BTCtoolshed/TheBox/MCU Settings.png

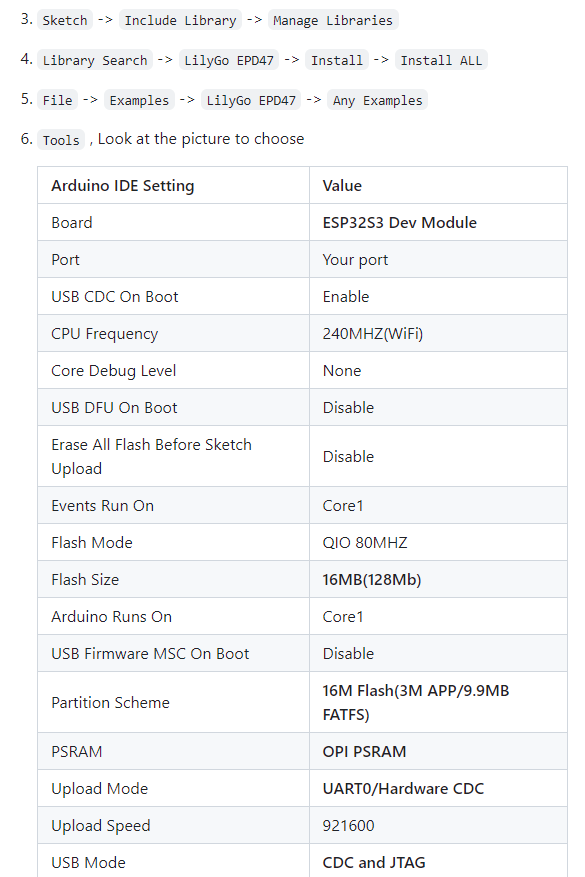
MCU Settings.png
