BTCtoolshed/TheBox/SourceLocation.png

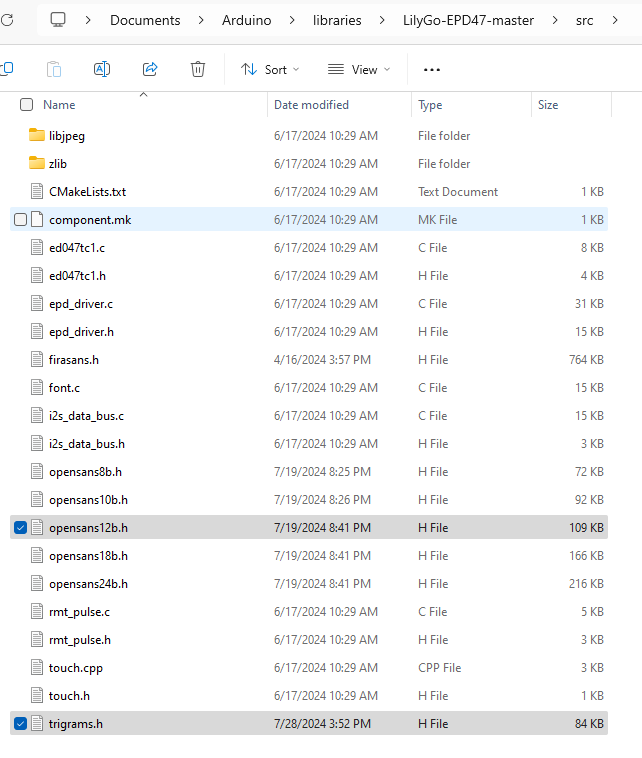
SourceLocation.png
