BTCtoolshed/TheBox/trigrams.h

const char string_0[] PROGMEM= "SPACE";
const char string_1[] PROGMEM= "a";
const char string_2[] PROGMEM= "abdomen";
const char string_3[] PROGMEM= "able/ability";
const char string_4[] PROGMEM= "abort-s-ed-ing";
const char string_5[] PROGMEM= "about";
const char string_6[] PROGMEM= "above";
const char string_7[] PROGMEM= "accident-al-s";
const char string_8[] PROGMEM= "accomplish-ed";
const char string_9[] PROGMEM= "accomplishing";
const char string_10[] PROGMEM= "ache";
const char string_11[] PROGMEM= "acknowledge";
const char string_12[] PROGMEM= "act-ion-ing-s";
const char string_13[] PROGMEM= "act-ive-ivity-s";
const char string_14[] PROGMEM= "add-ed-itional";
const char string_15[] PROGMEM= "add-ing-s";
const char string_16[] PROGMEM= "adjacent";
const char string_17[] PROGMEM= "administration";
const char string_18[] PROGMEM= "administrative";
const char string_19[] PROGMEM= "admit";
const char string_20[] PROGMEM= "advance-d-ing";
const char string_21[] PROGMEM= "after";
const char string_22[] PROGMEM= "age";
const char string_23[] PROGMEM= "agent-s";
const char string_24[] PROGMEM= "agree";
const char string_25[] PROGMEM= "air (fld/port)";
const char string_26[] PROGMEM= "airborne df";
const char string_27[] PROGMEM= "aircraft";
const char string_28[] PROGMEM= "airdrop-s";
const char string_29[] PROGMEM= "airmobile";
const char string_30[] PROGMEM= "alarm";
const char string_31[] PROGMEM= "ALE";
const char string_32[] PROGMEM= "alert-ed-ing";
const char string_33[] PROGMEM= "alive";
const char string_34[] PROGMEM= "all";
const char string_35[] PROGMEM= "alley";
const char string_36[] PROGMEM= "alt supply pt";
const char string_37[] PROGMEM= "alternate";
const char string_38[] PROGMEM= "alt ammo";
const char string_39[] PROGMEM= "altitude";
const char string_40[] PROGMEM= "am";
const char string_41[] PROGMEM= "am in pos (to)";
const char string_42[] PROGMEM= "amateur";
const char string_43[] PROGMEM= "ambulance";
const char string_44[] PROGMEM= "ambush-ed-ing";
const char string_45[] PROGMEM= "ammunition";
const char string_46[] PROGMEM= "amplitude modulation";
const char string_47[] PROGMEM= "amputate";
const char string_48[] PROGMEM= "an ";
const char string_49[] PROGMEM= "and";
const char string_50[] PROGMEM= "answer-d-ing-s";
const char string_51[] PROGMEM= "antenna";
const char string_52[] PROGMEM= "anti-";
const char string_53[] PROGMEM= "apply";
const char string_54[] PROGMEM= "approach-ed-s";
const char string_55[] PROGMEM= "approach-ing";
const char string_56[] PROGMEM= "approve-al-d-ing";
const char string_57[] PROGMEM= "approximate-ly";
const char string_58[] PROGMEM= "April";
const char string_59[] PROGMEM= "are/is";
const char string_60[] PROGMEM= "area-s";
const char string_61[] PROGMEM= "arm-s-ed";
const char string_62[] PROGMEM= "army-ies";
const char string_63[] PROGMEM= "around";
const char string_64[] PROGMEM= "arrange-d-ing";
const char string_65[] PROGMEM= "arrange-ment";
const char string_66[] PROGMEM= "arrive-al-d-ing";
const char string_67[] PROGMEM= "arrow";
const char string_68[] PROGMEM= "article";
const char string_69[] PROGMEM= "as";
const char string_70[] PROGMEM= "asap";
const char string_71[] PROGMEM= "ask";
const char string_72[] PROGMEM= "assault";
const char string_73[] PROGMEM= "assemble-d-ing";
const char string_74[] PROGMEM= "assist-ance";
const char string_75[] PROGMEM= "assist-ed-ing";
const char string_76[] PROGMEM= "at";
const char string_77[] PROGMEM= "at (once)";
const char string_78[] PROGMEM= "atlantic";
const char string_79[] PROGMEM= "attach-ed-ing";
const char string_80[] PROGMEM= "attach-ment";
const char string_81[] PROGMEM= "attack-ed-ing-s";
const char string_82[] PROGMEM= "August";
const char string_83[] PROGMEM= "authorization";
const char string_84[] PROGMEM= "authorize-d-ing";
const char string_85[] PROGMEM= "automatic";
const char string_86[] PROGMEM= "automobile";
const char string_87[] PROGMEM= "aviator/pilot";
const char string_88[] PROGMEM= "axe";
const char string_89[] PROGMEM= "axis (of)";
const char string_90[] PROGMEM= "azimuth (of)";
const char string_91[] PROGMEM= "b";
const char string_92[] PROGMEM= "back-ed-ing";
const char string_93[] PROGMEM= "bad";
const char string_94[] PROGMEM= "ball";
const char string_95[] PROGMEM= "band";
const char string_96[] PROGMEM= "bank";
const char string_97[] PROGMEM= "barbed wire";
const char string_98[] PROGMEM= "barometer";
const char string_99[] PROGMEM= "barrage-s";
const char string_100[] PROGMEM= "barrier";
const char string_101[] PROGMEM= "base-d-s-ing";
const char string_102[] PROGMEM= "battalion-s";
const char string_103[] PROGMEM= "battery charger";
const char string_104[] PROGMEM= "bed";
const char string_105[] PROGMEM= "been";
const char string_106[] PROGMEM= "beer";
const char string_107[] PROGMEM= "before";
const char string_108[] PROGMEM= "begin";
const char string_109[] PROGMEM= "below";
const char string_110[] PROGMEM= "belt";
const char string_111[] PROGMEM= "between";
const char string_112[] PROGMEM= "beyond";
const char string_113[] PROGMEM= "bike";
const char string_114[] PROGMEM= "binoculars";
const char string_115[] PROGMEM= "biological";
const char string_116[] PROGMEM= "bit";
const char string_117[] PROGMEM= "bite";
const char string_118[] PROGMEM= "bivouac-ed-ing";
const char string_119[] PROGMEM= "black";
const char string_120[] PROGMEM= "bleed";
const char string_121[] PROGMEM= "blister";
const char string_122[] PROGMEM= "block-ed-ing";
const char string_123[] PROGMEM= "blow-ing (up)";
const char string_124[] PROGMEM= "blow-n";
const char string_125[] PROGMEM= "blue";
const char string_126[] PROGMEM= "boat-s";
const char string_127[] PROGMEM= "bomb-d-r-ing-s";
const char string_128[] PROGMEM= "bone";
const char string_129[] PROGMEM= "boobytrap";
const char string_130[] PROGMEM= "book";
const char string_131[] PROGMEM= "boots";
const char string_132[] PROGMEM= "border";
const char string_133[] PROGMEM= "boundary-ies";
const char string_134[] PROGMEM= "bow";
const char string_135[] PROGMEM= "box";
const char string_136[] PROGMEM= "boy";
const char string_137[] PROGMEM= "break/broken";
const char string_138[] PROGMEM= "breakfast";
const char string_139[] PROGMEM= "breast";
const char string_140[] PROGMEM= "bridge-d-ing-s";
const char string_141[] PROGMEM= "brother";
const char string_142[] PROGMEM= "bug(s)";
const char string_143[] PROGMEM= "building-s";
const char string_144[] PROGMEM= "bulldozer";
const char string_145[] PROGMEM= "bunker-s";
const char string_146[] PROGMEM= "burst-ing-s";
const char string_147[] PROGMEM= "but";
const char string_148[] PROGMEM= "by";
const char string_149[] PROGMEM= "bypass-ed-ing-s";
const char string_150[] PROGMEM= "c";
const char string_151[] PROGMEM= "cable-s";
const char string_152[] PROGMEM= "cache";
const char string_153[] PROGMEM= "caliber";
const char string_154[] PROGMEM= "call";
const char string_155[] PROGMEM= "camera";
const char string_156[] PROGMEM= "camouflage-d";
const char string_157[] PROGMEM= "camouflage-ing";
const char string_158[] PROGMEM= "camp";
const char string_159[] PROGMEM= "can";
const char string_160[] PROGMEM= "can";
const char string_161[] PROGMEM= "canal-s";
const char string_162[] PROGMEM= "cancel-led-s";
const char string_163[] PROGMEM= "candle";
const char string_164[] PROGMEM= "capable-ity";
const char string_165[] PROGMEM= "capacity-ties";
const char string_166[] PROGMEM= "capsule";
const char string_167[] PROGMEM= "capture-d-ing";
const char string_168[] PROGMEM= "car";
const char string_169[] PROGMEM= "carry-ied-iers";
const char string_170[] PROGMEM= "casualty-ies";
const char string_171[] PROGMEM= "cave";
const char string_172[] PROGMEM= "CB radio";
const char string_173[] PROGMEM= "cease-s-d-ing";
const char string_174[] PROGMEM= "challenge-d-ing";
const char string_175[] PROGMEM= "chance";
const char string_176[] PROGMEM= "change";
const char string_177[] PROGMEM= "change cipher";
const char string_178[] PROGMEM= "channel";
const char string_179[] PROGMEM= "charge-d-s";
const char string_180[] PROGMEM= "check-d-ing-s";
const char string_181[] PROGMEM= "checkpoint";
const char string_182[] PROGMEM= "chemical-s";
const char string_183[] PROGMEM= "child-ren";
const char string_184[] PROGMEM= "church";
const char string_185[] PROGMEM= "circle";
const char string_186[] PROGMEM= "city";
const char string_187[] PROGMEM= "civilian-s";
const char string_188[] PROGMEM= "clarification(of)";
const char string_189[] PROGMEM= "class-ify";
const char string_190[] PROGMEM= "classification";
const char string_191[] PROGMEM= "clean-ed-ing";
const char string_192[] PROGMEM= "clear-ed-ance";
const char string_193[] PROGMEM= "clearing-s";
const char string_194[] PROGMEM= "close-d-ing";
const char string_195[] PROGMEM= "clothe-es-ing";
const char string_196[] PROGMEM= "coast-s-al";
const char string_197[] PROGMEM= "coffee";
const char string_198[] PROGMEM= "collapse";
const char string_199[] PROGMEM= "collect-ed-ion";
const char string_200[] PROGMEM= "collect-ing-s";
const char string_201[] PROGMEM= "column-s";
const char string_202[] PROGMEM= "combat";
const char string_203[] PROGMEM= "come-ing";
const char string_204[] PROGMEM= "comma";
const char string_205[] PROGMEM= "command-er-ed-ing-s";
const char string_206[] PROGMEM= "commit-ment";
const char string_207[] PROGMEM= "commit-ted-ing";
const char string_208[] PROGMEM= "communicate-d-ions-s";
const char string_209[] PROGMEM= "company";
const char string_210[] PROGMEM= "complete-d-ing";
const char string_211[] PROGMEM= "complete-ion";
const char string_212[] PROGMEM= "compound";
const char string_213[] PROGMEM= "compromise-d-ing";
const char string_214[] PROGMEM= "computer";
const char string_215[] PROGMEM= "concentrate-d-ing";
const char string_216[] PROGMEM= "concentrate-s-ion";
const char string_217[] PROGMEM= "condition-ed-ing";
const char string_218[] PROGMEM= "conduct-ed-ing";
const char string_219[] PROGMEM= "confidential";
const char string_220[] PROGMEM= "connect-ed-ing";
const char string_221[] PROGMEM= "connect-ion";
const char string_222[] PROGMEM= "conservation";
const char string_223[] PROGMEM= "conserve-d";
const char string_224[] PROGMEM= "consolidate-d";
const char string_225[] PROGMEM= "consolidate-ing";
const char string_226[] PROGMEM= "consolidation";
const char string_227[] PROGMEM= "contact-ed-s";
const char string_228[] PROGMEM= "contact-ing";
const char string_229[] PROGMEM= "contaminate-d";
const char string_230[] PROGMEM= "contaminate-ion-ing";
const char string_231[] PROGMEM= "continue-ation";
const char string_232[] PROGMEM= "continue-d-ing";
const char string_233[] PROGMEM= "control-ed-ing-s";
const char string_234[] PROGMEM= "conversation";
const char string_235[] PROGMEM= "convoy-s";
const char string_236[] PROGMEM= "cook";
const char string_237[] PROGMEM= "coord-s-d-ing";
const char string_238[] PROGMEM= "corporation";
const char string_239[] PROGMEM= "corps";
const char string_240[] PROGMEM= "correct (me)";
const char string_241[] PROGMEM= "correct-ed-ing";
const char string_242[] PROGMEM= "cost";
const char string_243[] PROGMEM= "could";
const char string_244[] PROGMEM= "counterattack-ed-s";
const char string_245[] PROGMEM= "counterattack-ing";
const char string_246[] PROGMEM= "counterpart";
const char string_247[] PROGMEM= "cover-ed-ing";
const char string_248[] PROGMEM= "craft";
const char string_249[] PROGMEM= "crane";
const char string_250[] PROGMEM= "critical-ly";
const char string_251[] PROGMEM= "cross-ed-ing";
const char string_252[] PROGMEM= "crossroad-s";
const char string_253[] PROGMEM= "crushed";
const char string_254[] PROGMEM= "crystal";
const char string_255[] PROGMEM= "CTCSS";
const char string_256[] PROGMEM= "culvert";
const char string_257[] PROGMEM= "cup";
const char string_258[] PROGMEM= "cut-off";
const char string_259[] PROGMEM= "CW";
const char string_260[] PROGMEM= "d";
const char string_261[] PROGMEM= "damage-d-ing";
const char string_262[] PROGMEM= "danger";
const char string_263[] PROGMEM= "dangerous";
const char string_264[] PROGMEM= "darkness";
const char string_265[] PROGMEM= "day-s/date-s";
const char string_266[] PROGMEM= "deadline-d-ing";
const char string_267[] PROGMEM= "death";
const char string_268[] PROGMEM= "December";
const char string_269[] PROGMEM= "deception";
const char string_270[] PROGMEM= "decontaminate-d-ion";
const char string_271[] PROGMEM= "decrease-d-ing";
const char string_272[] PROGMEM= "deer";
const char string_273[] PROGMEM= "defend-ed-g-s";
const char string_274[] PROGMEM= "defense-sive";
const char string_275[] PROGMEM= "degree-s";
const char string_276[] PROGMEM= "delay-ed-ing-s";
const char string_277[] PROGMEM= "delete-d-ion";
const char string_278[] PROGMEM= "deliver-ed-ing";
const char string_279[] PROGMEM= "demolition";
const char string_280[] PROGMEM= "demonstrate-d-ing";
const char string_281[] PROGMEM= "demonstrate-d-s-ion";
const char string_282[] PROGMEM= "deny-ied-ies";
const char string_283[] PROGMEM= "depart-ed-ing-ure";
const char string_284[] PROGMEM= "deploy-ed-ing";
const char string_285[] PROGMEM= "deploy-ment-s";
const char string_286[] PROGMEM= "depot";
const char string_287[] PROGMEM= "deputy-ies";
const char string_288[] PROGMEM= "designate-d";
const char string_289[] PROGMEM= "designate-ion";
const char string_290[] PROGMEM= "desk";
const char string_291[] PROGMEM= "destination";
const char string_292[] PROGMEM= "destroy-d-ing-s";
const char string_293[] PROGMEM= "detach-ed-es";
const char string_294[] PROGMEM= "detach-ment-s";
const char string_295[] PROGMEM= "determine";
const char string_296[] PROGMEM= "diesel";
const char string_297[] PROGMEM= "dig/dug (in)";
const char string_298[] PROGMEM= "dinner";
const char string_299[] PROGMEM= "direct-d-ion-ing";
const char string_300[] PROGMEM= "direction finding";
const char string_301[] PROGMEM= "disable-d-ing";
const char string_302[] PROGMEM= "disapprove-d-al";
const char string_303[] PROGMEM= "disperse-d-ing-al";
const char string_304[] PROGMEM= "displace-d-ing";
const char string_305[] PROGMEM= "displace-ment";
const char string_306[] PROGMEM= "dispose-d-al";
const char string_307[] PROGMEM= "disregard-ed-ing";
const char string_308[] PROGMEM= "distance-s";
const char string_309[] PROGMEM= "district-s";
const char string_310[] PROGMEM= "ditch";
const char string_311[] PROGMEM= "divert-ed-ion";
const char string_312[] PROGMEM= "divide";
const char string_313[] PROGMEM= "division-s";
const char string_314[] PROGMEM= "do";
const char string_315[] PROGMEM= "dog";
const char string_316[] PROGMEM= "down-ed";
const char string_317[] PROGMEM= "downed acft";
const char string_318[] PROGMEM= "drill drip";
const char string_319[] PROGMEM= "drive";
const char string_320[] PROGMEM= "driveway";
const char string_321[] PROGMEM= "drop-ping-ped";
const char string_322[] PROGMEM= "drug-s";
const char string_323[] PROGMEM= "DTMF";
const char string_324[] PROGMEM= "due";
const char string_325[] PROGMEM= "dump-ed-ing";
const char string_326[] PROGMEM= "during";
const char string_327[] PROGMEM= "e";
const char string_328[] PROGMEM= "east-ern (of)";
const char string_329[] PROGMEM= "ed";
const char string_330[] PROGMEM= "effect-ed-ing";
const char string_331[] PROGMEM= "effect-ive-s";
const char string_332[] PROGMEM= "eight";
const char string_333[] PROGMEM= "electric-al-ity";
const char string_334[] PROGMEM= "element-s";
const char string_335[] PROGMEM= "elevate-d-ion";
const char string_336[] PROGMEM= "eliminate-ed-ing-s";
const char string_337[] PROGMEM= "elk";
const char string_338[] PROGMEM= "email";
const char string_339[] PROGMEM= "embank-ment";
const char string_340[] PROGMEM= "embrace-d-ing";
const char string_341[] PROGMEM= "emergency";
const char string_342[] PROGMEM= "emplace-ment";
const char string_343[] PROGMEM= "employ-ed-ing";
const char string_344[] PROGMEM= "en";
const char string_345[] PROGMEM= "encounter-d-ing";
const char string_346[] PROGMEM= "encrypt-ed-ion";
const char string_347[] PROGMEM= "end-ed-ing";
const char string_348[] PROGMEM= "enemy";
const char string_349[] PROGMEM= "engine";
const char string_350[] PROGMEM= "engineer-d-ing-s";
const char string_351[] PROGMEM= "enlist-ed-ing";
const char string_352[] PROGMEM= "entrench-ed";
const char string_353[] PROGMEM= "envelop-ed-ing";
const char string_354[] PROGMEM= "envelope";
const char string_355[] PROGMEM= "equip-ing-s";
const char string_356[] PROGMEM= "er";
const char string_357[] PROGMEM= "error";
const char string_358[] PROGMEM= "es";
const char string_359[] PROGMEM= "escape-d-ing";
const char string_360[] PROGMEM= "estab-ed-contact at";
const char string_361[] PROGMEM= "establish";
const char string_362[] PROGMEM= "estimat-ion";
const char string_363[] PROGMEM= "estimate-d-ing";
const char string_364[] PROGMEM= "et";
const char string_365[] PROGMEM= "eta your loc";
const char string_366[] PROGMEM= "etd";
const char string_367[] PROGMEM= "evac-d-ing-ion";
const char string_368[] PROGMEM= "evasion";
const char string_369[] PROGMEM= "execute-d-ing";
const char string_370[] PROGMEM= "execute-ion-s";
const char string_371[] PROGMEM= "exercise";
const char string_372[] PROGMEM= "exhaust-ed-ing";
const char string_373[] PROGMEM= "expect-ation-s";
const char string_374[] PROGMEM= "expect-ed-ing";
const char string_375[] PROGMEM= "expedite-d-ing";
const char string_376[] PROGMEM= "explode-d-s";
const char string_377[] PROGMEM= "exploit-ed-ing";
const char string_378[] PROGMEM= "explosive-s";
const char string_379[] PROGMEM= "expose-d-ing";
const char string_380[] PROGMEM= "extend-d-g-ive";
const char string_381[] PROGMEM= "extend-extent";
const char string_382[] PROGMEM= "extend-sion";
const char string_383[] PROGMEM= "extra";
const char string_384[] PROGMEM= "extract-s-ed-ing";
const char string_385[] PROGMEM= "f";
const char string_386[] PROGMEM= "facility";
const char string_387[] PROGMEM= "fade-ed-ing";
const char string_388[] PROGMEM= "fail-ed-ing";
const char string_389[] PROGMEM= "fallout";
const char string_390[] PROGMEM= "family";
const char string_391[] PROGMEM= "far";
const char string_392[] PROGMEM= "fatal";
const char string_393[] PROGMEM= "father";
const char string_394[] PROGMEM= "favor-able-ing";
const char string_395[] PROGMEM= "favor-s-ed";
const char string_396[] PROGMEM= "February";
const char string_397[] PROGMEM= "feet/foot";
const char string_398[] PROGMEM= "FeldHell";
const char string_399[] PROGMEM= "FEMA";
const char string_400[] PROGMEM= "field-s";
const char string_401[] PROGMEM= "fight-er-ing";
const char string_402[] PROGMEM= "final";
const char string_403[] PROGMEM= "fire-d-ing-s";
const char string_404[] PROGMEM= "fish";
const char string_405[] PROGMEM= "five";
const char string_406[] PROGMEM= "flame-d-ing-s";
const char string_407[] PROGMEM= "flank-ed-ing-s";
const char string_408[] PROGMEM= "flare-d-s";
const char string_409[] PROGMEM= "fled";
const char string_410[] PROGMEM= "flesh";
const char string_411[] PROGMEM= "flexible-ity";
const char string_412[] PROGMEM= "flight";
const char string_413[] PROGMEM= "foe";
const char string_414[] PROGMEM= "fog";
const char string_415[] PROGMEM= "fold-ing";
const char string_416[] PROGMEM= "follow-ed-ing";
const char string_417[] PROGMEM= "food";
const char string_418[] PROGMEM= "for";
const char string_419[] PROGMEM= "force-s-d-ing";
const char string_420[] PROGMEM= "ford-able";
const char string_421[] PROGMEM= "forearm";
const char string_422[] PROGMEM= "forest-s";
const char string_423[] PROGMEM= "fortify-ication";
const char string_424[] PROGMEM= "fortify-ied";
const char string_425[] PROGMEM= "forward-ed-ing";
const char string_426[] PROGMEM= "found";
const char string_427[] PROGMEM= "four";
const char string_428[] PROGMEM= "fr";
const char string_429[] PROGMEM= "fracture";
const char string_430[] PROGMEM= "frag";
const char string_431[] PROGMEM= "freedom";
const char string_432[] PROGMEM= "freeze-ing";
const char string_433[] PROGMEM= "frequency modulation";
const char string_434[] PROGMEM= "frequency-ies";
const char string_435[] PROGMEM= "Friday";
const char string_436[] PROGMEM= "friend-ly";
const char string_437[] PROGMEM= "from";
const char string_438[] PROGMEM= "front-age-ally";
const char string_439[] PROGMEM= "FRS";
const char string_440[] PROGMEM= "fruit";
const char string_441[] PROGMEM= "fuel";
const char string_442[] PROGMEM= "fuse-d";
const char string_443[] PROGMEM= "future";
const char string_444[] PROGMEM= "g";
const char string_445[] PROGMEM= "gallon-s";
const char string_446[] PROGMEM= "gas-ing-ed";
const char string_447[] PROGMEM= "gasoline";
const char string_448[] PROGMEM= "gate";
const char string_449[] PROGMEM= "general-ize";
const char string_450[] PROGMEM= "generator(set)";
const char string_451[] PROGMEM= "get-ting";
const char string_452[] PROGMEM= "girl";
const char string_453[] PROGMEM= "give-n-ing";
const char string_454[] PROGMEM= "glass";
const char string_455[] PROGMEM= "GMRS";
const char string_456[] PROGMEM= "go-ing(to)";
const char string_457[] PROGMEM= "good";
const char string_458[] PROGMEM= "government";
const char string_459[] PROGMEM= "GPS";
const char string_460[] PROGMEM= "grade-d-ing";
const char string_461[] PROGMEM= "great";
const char string_462[] PROGMEM= "green";
const char string_463[] PROGMEM= "grid(coord)";
const char string_464[] PROGMEM= "ground-s-ed";
const char string_465[] PROGMEM= "group";
const char string_466[] PROGMEM= "guard-ed-ing-s";
const char string_467[] PROGMEM= "guide-ance";
const char string_468[] PROGMEM= "guide-d-s-ing";
const char string_469[] PROGMEM= "gunpowder";
const char string_470[] PROGMEM= "guns-s";
const char string_471[] PROGMEM= "h";
const char string_472[] PROGMEM= "had";
const char string_473[] PROGMEM= "halt-ed";
const char string_474[] PROGMEM= "Ham/ham";
const char string_475[] PROGMEM= "hammer";
const char string_476[] PROGMEM= "hand";
const char string_477[] PROGMEM= "handbook";
const char string_478[] PROGMEM= "handie-talkie";
const char string_479[] PROGMEM= "harass-ed-ing";
const char string_480[] PROGMEM= "harass-ment";
const char string_481[] PROGMEM= "hate";
const char string_482[] PROGMEM= "have/has";
const char string_483[] PROGMEM= "he";
const char string_484[] PROGMEM= "head-ed-ing";
const char string_485[] PROGMEM= "headphones";
const char string_486[] PROGMEM= "hear-d";
const char string_487[] PROGMEM= "heavy";
const char string_488[] PROGMEM= "held";
const char string_489[] PROGMEM= "helicopter-s";
const char string_490[] PROGMEM= "her";
const char string_491[] PROGMEM= "here";
const char string_492[] PROGMEM= "hidden";
const char string_493[] PROGMEM= "hide";
const char string_494[] PROGMEM= "high speed burst";
const char string_495[] PROGMEM= "high-er-est";
const char string_496[] PROGMEM= "highway-s";
const char string_497[] PROGMEM= "hill/mt/rise-s";
const char string_498[] PROGMEM= "him";
const char string_499[] PROGMEM= "his";
const char string_500[] PROGMEM= "hit-tin";
const char string_501[] PROGMEM= "hold-er-ing";
const char string_502[] PROGMEM= "hole";
const char string_503[] PROGMEM= "home";
const char string_504[] PROGMEM= "hospital-s";
const char string_505[] PROGMEM= "hostile";
const char string_506[] PROGMEM= "hour-s-ly";
const char string_507[] PROGMEM= "how";
const char string_508[] PROGMEM= "HQ";
const char string_509[] PROGMEM= "hundred";
const char string_510[] PROGMEM= "i";
const char string_511[] PROGMEM= "ice";
const char string_512[] PROGMEM= "identification";
const char string_513[] PROGMEM= "identify-ed";
const char string_514[] PROGMEM= "IDY";
const char string_515[] PROGMEM= "ied";
const char string_516[] PROGMEM= "ies";
const char string_517[] PROGMEM= "if";
const char string_518[] PROGMEM= "ill-ness";
const char string_519[] PROGMEM= "immediately";
const char string_520[] PROGMEM= "imminent";
const char string_521[] PROGMEM= "immobile-ize-d-ing";
const char string_522[] PROGMEM= "impact";
const char string_523[] PROGMEM= "impassible";
const char string_524[] PROGMEM= "impossible";
const char string_525[] PROGMEM= "improve-d-ing";
const char string_526[] PROGMEM= "improve-ment";
const char string_527[] PROGMEM= "improvised";
const char string_528[] PROGMEM= "in";
const char string_529[] PROGMEM= "in-accordance-with";
const char string_530[] PROGMEM= "inadequate";
const char string_531[] PROGMEM= "inch-es";
const char string_532[] PROGMEM= "incident-al-s";
const char string_533[] PROGMEM= "increase-d-ing-s";
const char string_534[] PROGMEM= "indigenous";
const char string_535[] PROGMEM= "indirect";
const char string_536[] PROGMEM= "individual";
const char string_537[] PROGMEM= "infantry";
const char string_538[] PROGMEM= "infiltrate-d-r-s";
const char string_539[] PROGMEM= "infiltrate-g-ion";
const char string_540[] PROGMEM= "inflict";
const char string_541[] PROGMEM= "inform-d-ation";
const char string_542[] PROGMEM= "infrared";
const char string_543[] PROGMEM= "ing";
const char string_544[] PROGMEM= "initial-ed-ly";
const char string_545[] PROGMEM= "insect";
const char string_546[] PROGMEM= "insert-s-ed-ing";
const char string_547[] PROGMEM= "install-d-ation";
const char string_548[] PROGMEM= "instrumental";
const char string_549[] PROGMEM= "intact";
const char string_550[] PROGMEM= "intend-ed-tion";
const char string_551[] PROGMEM= "intercept-d-or";
const char string_552[] PROGMEM= "intercept-ion-s";
const char string_553[] PROGMEM= "interfere-d-ing";
const char string_554[] PROGMEM= "interfere-nce";
const char string_555[] PROGMEM= "internal";
const char string_556[] PROGMEM= "interrogate-d";
const char string_557[] PROGMEM= "interrogate-ion";
const char string_558[] PROGMEM= "intersection";
const char string_559[] PROGMEM= "interval";
const char string_560[] PROGMEM= "is";
const char string_561[] PROGMEM= "isolate-d-ing";
const char string_562[] PROGMEM= "issue-d-ing-s";
const char string_563[] PROGMEM= "it";
const char string_564[] PROGMEM= "item-s";
const char string_565[] PROGMEM= "j";
const char string_566[] PROGMEM= "jacket";
const char string_567[] PROGMEM= "jam-med-ing";
const char string_568[] PROGMEM= "January";
const char string_569[] PROGMEM= "jeep";
const char string_570[] PROGMEM= "job";
const char string_571[] PROGMEM= "join-ed-ing";
const char string_572[] PROGMEM= "joint";
const char string_573[] PROGMEM= "July";
const char string_574[] PROGMEM= "jump-ed-ing (off)";
const char string_575[] PROGMEM= "junction-s(road)";
const char string_576[] PROGMEM= "June";
const char string_577[] PROGMEM= "jury";
const char string_578[] PROGMEM= "just";
const char string_579[] PROGMEM= "k";
const char string_580[] PROGMEM= "keep-s-ing";
const char string_581[] PROGMEM= "kerosene";
const char string_582[] PROGMEM= "key";
const char string_583[] PROGMEM= "kidney";
const char string_584[] PROGMEM= "kidney";
const char string_585[] PROGMEM= "kill";
const char string_586[] PROGMEM= "kill";
const char string_587[] PROGMEM= "killed in act";
const char string_588[] PROGMEM= "kilometer-s";
const char string_589[] PROGMEM= "kit";
const char string_590[] PROGMEM= "knife";
const char string_591[] PROGMEM= "knot";
const char string_592[] PROGMEM= "know-n-ing";
const char string_593[] PROGMEM= "knowledge";
const char string_594[] PROGMEM= "L";
const char string_595[] PROGMEM= "labor-ed-ing";
const char string_596[] PROGMEM= "lacerate";
const char string_597[] PROGMEM= "lamp";
const char string_598[] PROGMEM= "land-ed-ing";
const char string_599[] PROGMEM= "large";
const char string_600[] PROGMEM= "last";
const char string_601[] PROGMEM= "lateral";
const char string_602[] PROGMEM= "launch-d-r-ing";
const char string_603[] PROGMEM= "law";
const char string_604[] PROGMEM= "lay/laid";
const char string_605[] PROGMEM= "lead-er-ing";
const char string_606[] PROGMEM= "leaflet-s";
const char string_607[] PROGMEM= "least";
const char string_608[] PROGMEM= "leave/left";
const char string_609[] PROGMEM= "left (of)";
const char string_610[] PROGMEM= "leg";
const char string_611[] PROGMEM= "letter";
const char string_612[] PROGMEM= "level";
const char string_613[] PROGMEM= "liaison";
const char string_614[] PROGMEM= "library";
const char string_615[] PROGMEM= "life";
const char string_616[] PROGMEM= "ligh-er-ing-d-s";
const char string_617[] PROGMEM= "like-s";
const char string_618[] PROGMEM= "limit-ed-ing-s";
const char string_619[] PROGMEM= "line-d-s (of)";
const char string_620[] PROGMEM= "list";
const char string_621[] PROGMEM= "listen-ed-ing";
const char string_622[] PROGMEM= "litter-s";
const char string_623[] PROGMEM= "load-s-ed";
const char string_624[] PROGMEM= "local-ize-d";
const char string_625[] PROGMEM= "locate-d-ing-ions";
const char string_626[] PROGMEM= "location (of)";
const char string_627[] PROGMEM= "lock";
const char string_628[] PROGMEM= "log";
const char string_629[] PROGMEM= "logistic-al-s";
const char string_630[] PROGMEM= "look (for)";
const char string_631[] PROGMEM= "loss-es-t";
const char string_632[] PROGMEM= "loudspeaker";
const char string_633[] PROGMEM= "love";
const char string_634[] PROGMEM= "lowe-er-est";
const char string_635[] PROGMEM= "lower side band";
const char string_636[] PROGMEM= "lunch";
const char string_637[] PROGMEM= "ly";
const char string_638[] PROGMEM= "m";
const char string_639[] PROGMEM= "machinegun-s";
const char string_640[] PROGMEM= "made";
const char string_641[] PROGMEM= "magnetic";
const char string_642[] PROGMEM= "magnify-ing";
const char string_643[] PROGMEM= "main";
const char string_644[] PROGMEM= "main body";
const char string_645[] PROGMEM= "main supply rt";
const char string_646[] PROGMEM= "maintain-ed";
const char string_647[] PROGMEM= "maintain-ing-s";
const char string_648[] PROGMEM= "maintenance";
const char string_649[] PROGMEM= "make-ing/made";
const char string_650[] PROGMEM= "male";
const char string_651[] PROGMEM= "man-ned-ning";
const char string_652[] PROGMEM= "maneuver-ing-s";
const char string_653[] PROGMEM= "manual";
const char string_654[] PROGMEM= "many";
const char string_655[] PROGMEM= "map-ped-ping-s";
const char string_656[] PROGMEM= "March/march";
const char string_657[] PROGMEM= "market";
const char string_658[] PROGMEM= "MARS";
const char string_659[] PROGMEM= "match-ed-s-ing";
const char string_660[] PROGMEM= "max (range)";
const char string_661[] PROGMEM= "May";
const char string_662[] PROGMEM= "me";
const char string_663[] PROGMEM= "meal";
const char string_664[] PROGMEM= "means";
const char string_665[] PROGMEM= "measure-d";
const char string_666[] PROGMEM= "measurement";
const char string_667[] PROGMEM= "meat";
const char string_668[] PROGMEM= "mechanic-al";
const char string_669[] PROGMEM= "mechanize-d";
const char string_670[] PROGMEM= "medical";
const char string_671[] PROGMEM= "medium";
const char string_672[] PROGMEM= "medivac needed";
const char string_673[] PROGMEM= "meet (me at)";
const char string_674[] PROGMEM= "meet-ing";
const char string_675[] PROGMEM= "message-s";
const char string_676[] PROGMEM= "messenger";
const char string_677[] PROGMEM= "meter-s";
const char string_678[] PROGMEM= "MFSK";
const char string_679[] PROGMEM= "microphone";
const char string_680[] PROGMEM= "might";
const char string_681[] PROGMEM= "mile-s";
const char string_682[] PROGMEM= "milk";
const char string_683[] PROGMEM= "mine-d(field)";
const char string_684[] PROGMEM= "minimize-d";
const char string_685[] PROGMEM= "minimum";
const char string_686[] PROGMEM= "minor";
const char string_687[] PROGMEM= "minute(s)";
const char string_688[] PROGMEM= "miss-ed-ing";
const char string_689[] PROGMEM= "missile-s";
const char string_690[] PROGMEM= "missing in act";
const char string_691[] PROGMEM= "mission-s";
const char string_692[] PROGMEM= "mobile-ity";
const char string_693[] PROGMEM= "modem";
const char string_694[] PROGMEM= "modulation";
const char string_695[] PROGMEM= "Monday";
const char string_696[] PROGMEM= "money";
const char string_697[] PROGMEM= "moon";
const char string_698[] PROGMEM= "morale";
const char string_699[] PROGMEM= "more";
const char string_700[] PROGMEM= "morning";
const char string_701[] PROGMEM= "morse";
const char string_702[] PROGMEM= "most";
const char string_703[] PROGMEM= "mother";
const char string_704[] PROGMEM= "motor-ized";
const char string_705[] PROGMEM= "mount-ed-ing";
const char string_706[] PROGMEM= "mountain-ous";
const char string_707[] PROGMEM= "move-d-ing";
const char string_708[] PROGMEM= "move-ment";
const char string_709[] PROGMEM= "MRE";
const char string_710[] PROGMEM= "multiple";
const char string_711[] PROGMEM= "music";
const char string_712[] PROGMEM= "my";
const char string_713[] PROGMEM= "my location is";
const char string_714[] PROGMEM= "n";
const char string_715[] PROGMEM= "nail";
const char string_716[] PROGMEM= "narrow";
const char string_717[] PROGMEM= "near";
const char string_718[] PROGMEM= "need-ed-ing";
const char string_719[] PROGMEM= "net-ted-ing";
const char string_720[] PROGMEM= "network";
const char string_721[] PROGMEM= "neutral";
const char string_722[] PROGMEM= "neutralize-d-ing";
const char string_723[] PROGMEM= "new";
const char string_724[] PROGMEM= "news";
const char string_725[] PROGMEM= "newspaper";
const char string_726[] PROGMEM= "night vision";
const char string_727[] PROGMEM= "night-s";
const char string_728[] PROGMEM= "nine";
const char string_729[] PROGMEM= "no fire line";
const char string_730[] PROGMEM= "no/non/neg";
const char string_731[] PROGMEM= "none";
const char string_732[] PROGMEM= "north-ern(of)";
const char string_733[] PROGMEM= "not";
const char string_734[] PROGMEM= "not later than";
const char string_735[] PROGMEM= "note";
const char string_736[] PROGMEM= "notebook";
const char string_737[] PROGMEM= "nothing";
const char string_738[] PROGMEM= "notify-ed-s";
const char string_739[] PROGMEM= "November";
const char string_740[] PROGMEM= "now";
const char string_741[] PROGMEM= "nuclear";
const char string_742[] PROGMEM= "number-s";
const char string_743[] PROGMEM= "o";
const char string_744[] PROGMEM= "objective-s";
const char string_745[] PROGMEM= "observation post";
const char string_746[] PROGMEM= "observation-s";
const char string_747[] PROGMEM= "observe-d-r";
const char string_748[] PROGMEM= "observe-s-ing";
const char string_749[] PROGMEM= "obstacle-s";
const char string_750[] PROGMEM= "occupy-ed-ing";
const char string_751[] PROGMEM= "October";
const char string_752[] PROGMEM= "odor";
const char string_753[] PROGMEM= "of";
const char string_754[] PROGMEM= "offense-ive";
const char string_755[] PROGMEM= "officer-s";
const char string_756[] PROGMEM= "oil";
const char string_757[] PROGMEM= "on";
const char string_758[] PROGMEM= "one";
const char string_759[] PROGMEM= "only";
const char string_760[] PROGMEM= "open-ed-ing";
const char string_761[] PROGMEM= "operate-s-d-ing";
const char string_762[] PROGMEM= "operation-al";
const char string_763[] PROGMEM= "opportunity-s";
const char string_764[] PROGMEM= "or";
const char string_765[] PROGMEM= "orange";
const char string_766[] PROGMEM= "order-ed";
const char string_767[] PROGMEM= "ordnance";
const char string_768[] PROGMEM= "organize-ation";
const char string_769[] PROGMEM= "organize-d";
const char string_770[] PROGMEM= "orient-ing-ation";
const char string_771[] PROGMEM= "origin-al-ate";
const char string_772[] PROGMEM= "other";
const char string_773[] PROGMEM= "our";
const char string_774[] PROGMEM= "out (of)";
const char string_775[] PROGMEM= "outpost";
const char string_776[] PROGMEM= "over-age";
const char string_777[] PROGMEM= "over-run";
const char string_778[] PROGMEM= "overlay";
const char string_779[] PROGMEM= "own";
const char string_780[] PROGMEM= "p";
const char string_781[] PROGMEM= "pacific";
const char string_782[] PROGMEM= "packet";
const char string_783[] PROGMEM= "PACTOR";
const char string_784[] PROGMEM= "panel-s";
const char string_785[] PROGMEM= "pants";
const char string_786[] PROGMEM= "paratroop-s";
const char string_787[] PROGMEM= "part-s";
const char string_788[] PROGMEM= "party-s";
const char string_789[] PROGMEM= "pass-able";
const char string_790[] PROGMEM= "pass-age-ing";
const char string_791[] PROGMEM= "password";
const char string_792[] PROGMEM= "past";
const char string_793[] PROGMEM= "patrol-ed-ing-s";
const char string_794[] PROGMEM= "PBBS";
const char string_795[] PROGMEM= "pen";
const char string_796[] PROGMEM= "pencil";
const char string_797[] PROGMEM= "penetrate-d-ing";
const char string_798[] PROGMEM= "penetration";
const char string_799[] PROGMEM= "people";
const char string_800[] PROGMEM= "pepper";
const char string_801[] PROGMEM= "per";
const char string_802[] PROGMEM= "percent-age";
const char string_803[] PROGMEM= "perimeter";
const char string_804[] PROGMEM= "period";
const char string_805[] PROGMEM= "permission";
const char string_806[] PROGMEM= "permit-ed-ing";
const char string_807[] PROGMEM= "PGP";
const char string_808[] PROGMEM= "phase";
const char string_809[] PROGMEM= "photo-er-ed-ing";
const char string_810[] PROGMEM= "pick";
const char string_811[] PROGMEM= "pick (up)";
const char string_812[] PROGMEM= "piece-d-ing-s";
const char string_813[] PROGMEM= "pipeline";
const char string_814[] PROGMEM= "pistol";
const char string_815[] PROGMEM= "place-d-ing";
const char string_816[] PROGMEM= "plan-s-ed-ing";
const char string_817[] PROGMEM= "platoons";
const char string_818[] PROGMEM= "point-s-ed-ing";
const char string_819[] PROGMEM= "police";
const char string_820[] PROGMEM= "port(harbor)";
const char string_821[] PROGMEM= "position-s-ed";
const char string_822[] PROGMEM= "possible";
const char string_823[] PROGMEM= "post office";
const char string_824[] PROGMEM= "post-s";
const char string_825[] PROGMEM= "postpone-s-ed-ing";
const char string_826[] PROGMEM= "pound-s";
const char string_827[] PROGMEM= "powder";
const char string_828[] PROGMEM= "preparation";
const char string_829[] PROGMEM= "prepare-d-ing-s";
const char string_830[] PROGMEM= "prevent";
const char string_831[] PROGMEM= "priest";
const char string_832[] PROGMEM= "primary";
const char string_833[] PROGMEM= "print";
const char string_834[] PROGMEM= "printer";
const char string_835[] PROGMEM= "priority";
const char string_836[] PROGMEM= "privacy";
const char string_837[] PROGMEM= "private";
const char string_838[] PROGMEM= "prize-s of war";
const char string_839[] PROGMEM= "probable";
const char string_840[] PROGMEM= "process-ed-ing";
const char string_841[] PROGMEM= "professional";
const char string_842[] PROGMEM= "progress-ed-ing";
const char string_843[] PROGMEM= "propane";
const char string_844[] PROGMEM= "protect-ed-s-ing";
const char string_845[] PROGMEM= "protect-ive";
const char string_846[] PROGMEM= "protection";
const char string_847[] PROGMEM= "provide-d-ing";
const char string_848[] PROGMEM= "province";
const char string_849[] PROGMEM= "provision";
const char string_850[] PROGMEM= "PSK";
const char string_851[] PROGMEM= "psych";
const char string_852[] PROGMEM= "pure";
const char string_853[] PROGMEM= "purification";
const char string_854[] PROGMEM= "purple";
const char string_855[] PROGMEM= "pursue-d-ing-t";
const char string_856[] PROGMEM= "put";
const char string_857[] PROGMEM= "q";
const char string_858[] PROGMEM= "quell";
const char string_859[] PROGMEM= "quest";
const char string_860[] PROGMEM= "question-ed";
const char string_861[] PROGMEM= "quiet";
const char string_862[] PROGMEM= "quit";
const char string_863[] PROGMEM= "quiz";
const char string_864[] PROGMEM= "r";
const char string_865[] PROGMEM= "rad(rad/hr)";
const char string_866[] PROGMEM= "radar";
const char string_867[] PROGMEM= "radiation";
const char string_868[] PROGMEM= "radiator";
const char string_869[] PROGMEM= "radio-s";
const char string_870[] PROGMEM= "radiological";
const char string_871[] PROGMEM= "raid-er-ing-s";
const char string_872[] PROGMEM= "railhead";
const char string_873[] PROGMEM= "railroad-s";
const char string_874[] PROGMEM= "rain";
const char string_875[] PROGMEM= "range";
const char string_876[] PROGMEM= "rate";
const char string_877[] PROGMEM= "ration-s-ed";
const char string_878[] PROGMEM= "reach-ed-s-ing";
const char string_879[] PROGMEM= "read";
const char string_880[] PROGMEM= "ready";
const char string_881[] PROGMEM= "rear";
const char string_882[] PROGMEM= "receive-d-er-ing";
const char string_883[] PROGMEM= "recognize-d-ing";
const char string_884[] PROGMEM= "recon";
const char string_885[] PROGMEM= "record";
const char string_886[] PROGMEM= "recorder";
const char string_887[] PROGMEM= "recover-ed-y";
const char string_888[] PROGMEM= "red";
const char string_889[] PROGMEM= "reduce-ing-tion";
const char string_890[] PROGMEM= "reference-d-s";
const char string_891[] PROGMEM= "reference(to)";
const char string_892[] PROGMEM= "refuge";
const char string_893[] PROGMEM= "refugee(s)";
const char string_894[] PROGMEM= "regiment-ed-s";
const char string_895[] PROGMEM= "registration";
const char string_896[] PROGMEM= "regroup-ed-ing";
const char string_897[] PROGMEM= "reinf-ed-s-ing";
const char string_898[] PROGMEM= "reinforcement(s)";
const char string_899[] PROGMEM= "relay-ed-ing";
const char string_900[] PROGMEM= "release-d-ing-s";
const char string_901[] PROGMEM= "relief/relive";
const char string_902[] PROGMEM= "remain-ing";
const char string_903[] PROGMEM= "rendezvous";
const char string_904[] PROGMEM= "reorganize-d-ation-s";
const char string_905[] PROGMEM= "repair-ed-ing";
const char string_906[] PROGMEM= "repeat-ed-ing";
const char string_907[] PROGMEM= "repeater (radio)";
const char string_908[] PROGMEM= "repel-ed-ing-s";
const char string_909[] PROGMEM= "replace-d-ing-s";
const char string_910[] PROGMEM= "replacement";
const char string_911[] PROGMEM= "report-ed-ing";
const char string_912[] PROGMEM= "report-s(to)";
const char string_913[] PROGMEM= "repulse-d-ing";
const char string_914[] PROGMEM= "request-d-ing-s";
const char string_915[] PROGMEM= "require-d-ing";
const char string_916[] PROGMEM= "requirement";
const char string_917[] PROGMEM= "rescue";
const char string_918[] PROGMEM= "reserve-d-ing-s";
const char string_919[] PROGMEM= "resist-ing-ed";
const char string_920[] PROGMEM= "resistance";
const char string_921[] PROGMEM= "rest";
const char string_922[] PROGMEM= "restore-d-s";
const char string_923[] PROGMEM= "restrict-ion";
const char string_924[] PROGMEM= "restrictive";
const char string_925[] PROGMEM= "result-s-ed-ing";
const char string_926[] PROGMEM= "resupply-d-s-ing";
const char string_927[] PROGMEM= "return-ed-ing";
const char string_928[] PROGMEM= "ridge-d-s";
const char string_929[] PROGMEM= "rifle-s";
const char string_930[] PROGMEM= "right(of)";
const char string_931[] PROGMEM= "riot-s-ed";
const char string_932[] PROGMEM= "river-stream-s";
const char string_933[] PROGMEM= "road-s";
const char string_934[] PROGMEM= "roadblock";
const char string_935[] PROGMEM= "round-s";
const char string_936[] PROGMEM= "route-s-d-ing";
const char string_937[] PROGMEM= "RTTY";
const char string_938[] PROGMEM= "rucksack";
const char string_939[] PROGMEM= "rug";
const char string_940[] PROGMEM= "ruin-s-ed";
const char string_941[] PROGMEM= "s";
const char string_942[] PROGMEM= "sad";
const char string_943[] PROGMEM= "safe-r-ty";
const char string_944[] PROGMEM= "said";
const char string_945[] PROGMEM= "salt";
const char string_946[] PROGMEM= "Saturday";
const char string_947[] PROGMEM= "saw";
const char string_948[] PROGMEM= "schedule-d-ing-s";
const char string_949[] PROGMEM= "school";
const char string_950[] PROGMEM= "scope";
const char string_951[] PROGMEM= "scout-ed-ing-s";
const char string_952[] PROGMEM= "screen-d-ing-s";
const char string_953[] PROGMEM= "search-d-ing-s";
const char string_954[] PROGMEM= "second-s-ary";
const char string_955[] PROGMEM= "secret";
const char string_956[] PROGMEM= "section-s";
const char string_957[] PROGMEM= "sector-s";
const char string_958[] PROGMEM= "secure-d-ing";
const char string_959[] PROGMEM= "security";
const char string_960[] PROGMEM= "send/sent-ing";
const char string_961[] PROGMEM= "separate-d-ion";
const char string_962[] PROGMEM= "September";
const char string_963[] PROGMEM= "sequence";
const char string_964[] PROGMEM= "service-d-able";
const char string_965[] PROGMEM= "seven";
const char string_966[] PROGMEM= "shall";
const char string_967[] PROGMEM= "shell-s-ing-ed";
const char string_968[] PROGMEM= "shell-s-ing-ed";
const char string_969[] PROGMEM= "shelter";
const char string_970[] PROGMEM= "shelter";
const char string_971[] PROGMEM= "shirt";
const char string_972[] PROGMEM= "shirt";
const char string_973[] PROGMEM= "shoot-ing/shot";
const char string_974[] PROGMEM= "short-ed";
const char string_975[] PROGMEM= "shortwave";
const char string_976[] PROGMEM= "shoulder";
const char string_977[] PROGMEM= "sick";
const char string_978[] PROGMEM= "sieze-d-ing";
const char string_979[] PROGMEM= "siezure-s";
const char string_980[] PROGMEM= "sight-ed-ing";
const char string_981[] PROGMEM= "sign-ed-ing";
const char string_982[] PROGMEM= "signal-ed-ing";
const char string_983[] PROGMEM= "silent-ly-ce";
const char string_984[] PROGMEM= "simplex";
const char string_985[] PROGMEM= "simulate-d-ing";
const char string_986[] PROGMEM= "sister";
const char string_987[] PROGMEM= "sit/sitrep";
const char string_988[] PROGMEM= "site-s";
const char string_989[] PROGMEM= "six";
const char string_990[] PROGMEM= "sleep-ing";
const char string_991[] PROGMEM= "slope-s-ing-d";
const char string_992[] PROGMEM= "slow-ed-ing";
const char string_993[] PROGMEM= "small-er-est";
const char string_994[] PROGMEM= "smoke-d-ing-s";
const char string_995[] PROGMEM= "sniper";
const char string_996[] PROGMEM= "snow";
const char string_997[] PROGMEM= "so";
const char string_998[] PROGMEM= "socks";
const char string_999[] PROGMEM= "solar";
const char string_1000[] PROGMEM= "solder";
const char string_1001[] PROGMEM= "soldier";
const char string_1002[] PROGMEM= "some";
const char string_1003[] PROGMEM= "soon-er-est";
const char string_1004[] PROGMEM= "sorry";
const char string_1005[] PROGMEM= "sortie-s";
const char string_1006[] PROGMEM= "south-ern(of)";
const char string_1007[] PROGMEM= "speak";
const char string_1008[] PROGMEM= "spearhead";
const char string_1009[] PROGMEM= "spice";
const char string_1010[] PROGMEM= "spine";
const char string_1011[] PROGMEM= "sporadic";
const char string_1012[] PROGMEM= "spot-ted";
const char string_1013[] PROGMEM= "squad-s";
const char string_1014[] PROGMEM= "stand-ing(by)";
const char string_1015[] PROGMEM= "start-ed-ing";
const char string_1016[] PROGMEM= "station-ed-s";
const char string_1017[] PROGMEM= "status(report)";
const char string_1018[] PROGMEM= "stay-ed-ing";
const char string_1019[] PROGMEM= "stike/struck";
const char string_1020[] PROGMEM= "stole-n";
const char string_1021[] PROGMEM= "stop-ped-ing";
const char string_1022[] PROGMEM= "storm";
const char string_1023[] PROGMEM= "storm-ing-s";
const char string_1024[] PROGMEM= "street";
const char string_1025[] PROGMEM= "strength-en";
const char string_1026[] PROGMEM= "strong-er-est";
const char string_1027[] PROGMEM= "submit-ed-ing";
const char string_1028[] PROGMEM= "success-ful-ly";
const char string_1029[] PROGMEM= "such";
const char string_1030[] PROGMEM= "Sunday";
const char string_1031[] PROGMEM= "sunrise";
const char string_1032[] PROGMEM= "sunset";
const char string_1033[] PROGMEM= "superior-ity";
const char string_1034[] PROGMEM= "supplement-ed-ary";
const char string_1035[] PROGMEM= "supply-d-s-ing";
const char string_1036[] PROGMEM= "surface-d-ing";
const char string_1037[] PROGMEM= "surgey";
const char string_1038[] PROGMEM= "surround-ed-ing";
const char string_1039[] PROGMEM= "surveillance";
const char string_1040[] PROGMEM= "survey-ed-s";
const char string_1041[] PROGMEM= "survival";
const char string_1042[] PROGMEM= "suspect-ed-ing";
const char string_1043[] PROGMEM= "swallow-ed(s)";
const char string_1044[] PROGMEM= "switch-ed-ing";
const char string_1045[] PROGMEM= "swollen";
const char string_1046[] PROGMEM= "symmetric";
const char string_1047[] PROGMEM= "t";
const char string_1048[] PROGMEM= "tablet";
const char string_1049[] PROGMEM= "tactic-s-al";
const char string_1050[] PROGMEM= "take-ing/took";
const char string_1051[] PROGMEM= "talk";
const char string_1052[] PROGMEM= "tank destroyer-s";
const char string_1053[] PROGMEM= "tank-er-s";
const char string_1054[] PROGMEM= "tape";
const char string_1055[] PROGMEM= "target-s";
const char string_1056[] PROGMEM= "task(force)";
const char string_1057[] PROGMEM= "taxi";
const char string_1058[] PROGMEM= "team-s-ed";
const char string_1059[] PROGMEM= "tear gas";
const char string_1060[] PROGMEM= "ted";
const char string_1061[] PROGMEM= "teen";
const char string_1062[] PROGMEM= "teeth";
const char string_1063[] PROGMEM= "telephone-s";
const char string_1064[] PROGMEM= "television";
const char string_1065[] PROGMEM= "temple";
const char string_1066[] PROGMEM= "tentative";
const char string_1067[] PROGMEM= "terminate-d-ing";
const char string_1068[] PROGMEM= "terrain";
const char string_1069[] PROGMEM= "territory";
const char string_1070[] PROGMEM= "terrorism";
const char string_1071[] PROGMEM= "terrorists";
const char string_1072[] PROGMEM= "that";
const char string_1073[] PROGMEM= "the";
const char string_1074[] PROGMEM= "their";
const char string_1075[] PROGMEM= "them";
const char string_1076[] PROGMEM= "then";
const char string_1077[] PROGMEM= "there";
const char string_1078[] PROGMEM= "these";
const char string_1079[] PROGMEM= "they";
const char string_1080[] PROGMEM= "this";
const char string_1081[] PROGMEM= "those";
const char string_1082[] PROGMEM= "thousand";
const char string_1083[] PROGMEM= "three";
const char string_1084[] PROGMEM= "THROB";
const char string_1085[] PROGMEM= "through";
const char string_1086[] PROGMEM= "thunder";
const char string_1087[] PROGMEM= "Thursday";
const char string_1088[] PROGMEM= "tide";
const char string_1089[] PROGMEM= "time";
const char string_1090[] PROGMEM= "time-d-ing";
const char string_1091[] PROGMEM= "tion";
const char string_1092[] PROGMEM= "tire";
const char string_1093[] PROGMEM= "to(be)";
const char string_1094[] PROGMEM= "today";
const char string_1095[] PROGMEM= "tomorrow";
const char string_1096[] PROGMEM= "ton-s-age";
const char string_1097[] PROGMEM= "tone";
const char string_1098[] PROGMEM= "tonight";
const char string_1099[] PROGMEM= "tooth";
const char string_1100[] PROGMEM= "top secret";
const char string_1101[] PROGMEM= "total";
const char string_1102[] PROGMEM= "tow-ed-ing";
const char string_1103[] PROGMEM= "toward";
const char string_1104[] PROGMEM= "town/village-s";
const char string_1105[] PROGMEM= "trace-r";
const char string_1106[] PROGMEM= "track-ed-ing";
const char string_1107[] PROGMEM= "traffic";
const char string_1108[] PROGMEM= "trail-er-d-ing-s";
const char string_1109[] PROGMEM= "train-ed-ing-s";
const char string_1110[] PROGMEM= "transmission";
const char string_1111[] PROGMEM= "transmit-ed";
const char string_1112[] PROGMEM= "transport-ed";
const char string_1113[] PROGMEM= "transport-ing-s";
const char string_1114[] PROGMEM= "transportation";
const char string_1115[] PROGMEM= "trapped";
const char string_1116[] PROGMEM= "trouble";
const char string_1117[] PROGMEM= "truck-ed-s-ing";
const char string_1118[] PROGMEM= "Tuesday";
const char string_1119[] PROGMEM= "turn-ed-ing";
const char string_1120[] PROGMEM= "two";
const char string_1121[] PROGMEM= "u";
const char string_1122[] PROGMEM= "unable";
const char string_1123[] PROGMEM= "unarmed";
const char string_1124[] PROGMEM= "unauthorized";
const char string_1125[] PROGMEM= "under";
const char string_1126[] PROGMEM= "undercover";
const char string_1127[] PROGMEM= "understand";
const char string_1128[] PROGMEM= "understood";
const char string_1129[] PROGMEM= "unharmed";
const char string_1130[] PROGMEM= "unidentified";
const char string_1131[] PROGMEM= "unite-d-s-ing";
const char string_1132[] PROGMEM= "until(further notice)";
const char string_1133[] PROGMEM= "unusual";
const char string_1134[] PROGMEM= "up";
const char string_1135[] PROGMEM= "upper side band";
const char string_1136[] PROGMEM= "us";
const char string_1137[] PROGMEM= "use-d-g";
const char string_1138[] PROGMEM= "UTC";
const char string_1139[] PROGMEM= "v";
const char string_1140[] PROGMEM= "vaccine";
const char string_1141[] PROGMEM= "valley";
const char string_1142[] PROGMEM= "vegetable";
const char string_1143[] PROGMEM= "vehicle";
const char string_1144[] PROGMEM= "verification";
const char string_1145[] PROGMEM= "verify-ied";
const char string_1146[] PROGMEM= "very";
const char string_1147[] PROGMEM= "video";
const char string_1148[] PROGMEM= "violate-s-d";
const char string_1149[] PROGMEM= "violet";
const char string_1150[] PROGMEM= "virus";
const char string_1151[] PROGMEM= "visible-ity";
const char string_1152[] PROGMEM= "volt-s";
const char string_1153[] PROGMEM= "voltage";
const char string_1154[] PROGMEM= "vulnerable";
const char string_1155[] PROGMEM= "w";
const char string_1156[] PROGMEM= "wagon";
const char string_1157[] PROGMEM= "wait-ed-ing";
const char string_1158[] PROGMEM= "war";
const char string_1159[] PROGMEM= "warehouse";
const char string_1160[] PROGMEM= "was/were";
const char string_1161[] PROGMEM= "water";
const char string_1162[] PROGMEM= "watts";
const char string_1163[] PROGMEM= "wax";
const char string_1164[] PROGMEM= "waypoint";
const char string_1165[] PROGMEM= "we/us";
const char string_1166[] PROGMEM= "weak-en-ness";
const char string_1167[] PROGMEM= "weapon-s";
const char string_1168[] PROGMEM= "weather";
const char string_1169[] PROGMEM= "Wednesday";
const char string_1170[] PROGMEM= "week-s";
const char string_1171[] PROGMEM= "weekend";
const char string_1172[] PROGMEM= "well";
const char string_1173[] PROGMEM= "west-ern(of)";
const char string_1174[] PROGMEM= "what";
const char string_1175[] PROGMEM= "wheel-ed";
const char string_1176[] PROGMEM= "when";
const char string_1177[] PROGMEM= "where";
const char string_1178[] PROGMEM= "which";
const char string_1179[] PROGMEM= "white";
const char string_1180[] PROGMEM= "who";
const char string_1181[] PROGMEM= "wife";
const char string_1182[] PROGMEM= "wild";
const char string_1183[] PROGMEM= "wilderness";
const char string_1184[] PROGMEM= "will";
const char string_1185[] PROGMEM= "wind";
const char string_1186[] PROGMEM= "WinLink";
const char string_1187[] PROGMEM= "wire-s-d-ing";
const char string_1188[] PROGMEM= "with";
const char string_1189[] PROGMEM= "withdraw-ing-s";
const char string_1190[] PROGMEM= "wood-s-ed";
const char string_1191[] PROGMEM= "work-s-ed-ing";
const char string_1192[] PROGMEM= "Y";
const char string_1193[] PROGMEM= "yellow";
const char string_1194[] PROGMEM= "yet";
const char string_1195[] PROGMEM= "your-r";
const char string_1196[] PROGMEM= "z";
const char string_1197[] PROGMEM= "zero";
const char string_1198[] PROGMEM= "zone-s-ing";

const char *const TRIGRAMS [] PROGMEM = {string_0,string_1,string_2,string_3,string_4,string_5,string_6,string_7,string_8,string_9,string_10,string_11,string_12,string_13,string_14,string_15,string_16,string_17,string_18,string_19,string_20,string_21,string_22,string_23,string_24,string_25,string_26,string_27,string_28,string_29,string_30,string_31,string_32,string_33,string_34,string_35,string_36,string_37,string_38,string_39,string_40,string_41,string_42,string_43,string_44,string_45,string_46,string_47,string_48,string_49,string_50,string_51,string_52,string_53,string_54,string_55,string_56,string_57,string_58,string_59,string_60,string_61,string_62,string_63,string_64,string_65,string_66,string_67,string_68,string_69,string_70,string_71,string_72,string_73,string_74,string_75,string_76,string_77,string_78,string_79,string_80,string_81,string_82,string_83,string_84,string_85,string_86,string_87,string_88,string_89,string_90,string_91,string_92,string_93,string_94,string_95,string_96,string_97,string_98,string_99,string_100,string_101,string_102,string_103,string_104,string_105,string_106,string_107,string_108,string_109,string_110,string_111,string_112,string_113,string_114,string_115,string_116,string_117,string_118,string_119,string_120,string_121,string_122,string_123,string_124,string_125,string_126,string_127,string_128,string_129,string_130,string_131,string_132,string_133,string_134,string_135,string_136,string_137,string_138,string_139,string_140,string_141,string_142,string_143,string_144,string_145,string_146,string_147,string_148,string_149,string_150,string_151,string_152,string_153,string_154,string_155,string_156,string_157,string_158,string_159,string_160,string_161,string_162,string_163,string_164,string_165,string_166,string_167,string_168,string_169,string_170,string_171,string_172,string_173,string_174,string_175,string_176,string_177,string_178,string_179,string_180,string_181,string_182,string_183,string_184,string_185,string_186,string_187,string_188,string_189,string_190,string_191,string_192,string_193,string_194,string_195,string_196,string_197,string_198,string_199,string_200,string_201,string_202,string_203,string_204,string_205,string_206,string_207,string_208,string_209,string_210,string_211,string_212,string_213,string_214,string_215,string_216,string_217,string_218,string_219,string_220,string_221,string_222,string_223,string_224,string_225,string_226,string_227,string_228,string_229,string_230,string_231,string_232,string_233,string_234,string_235,string_236,string_237,string_238,string_239,string_240,string_241,string_242,string_243,string_244,string_245,string_246,string_247,string_248,string_249,string_250,string_251,string_252,string_253,string_254,string_255,string_256,string_257,string_258,string_259,string_260,string_261,string_262,string_263,string_264,string_265,string_266,string_267,string_268,string_269,string_270,string_271,string_272,string_273,string_274,string_275,string_276,string_277,string_278,string_279,string_280,string_281,string_282,string_283,string_284,string_285,string_286,string_287,string_288,string_289,string_290,string_291,string_292,string_293,string_294,string_295,string_296,string_297,string_298,string_299,string_300,string_301,string_302,string_303,string_304,string_305,string_306,string_307,string_308,string_309,string_310,string_311,string_312,string_313,string_314,string_315,string_316,string_317,string_318,string_319,string_320,string_321,string_322,string_323,string_324,string_325,string_326,string_327,string_328,string_329,string_330,string_331,string_332,string_333,string_334,string_335,string_336,string_337,string_338,string_339,string_340,string_341,string_342,string_343,string_344,string_345,string_346,string_347,string_348,string_349,string_350,string_351,string_352,string_353,string_354,string_355,string_356,string_357,string_358,string_359,string_360,string_361,string_362,string_363,string_364,string_365,string_366,string_367,string_368,string_369,string_370,string_371,string_372,string_373,string_374,string_375,string_376,string_377,string_378,string_379,string_380,string_381,string_382,string_383,string_384,string_385,string_386,string_387,string_388,string_389,string_390,string_391,string_392,string_393,string_394,string_395,string_396,string_397,string_398,string_399,string_400,string_401,string_402,string_403,string_404,string_405,string_406,string_407,string_408,string_409,string_410,string_411,string_412,string_413,string_414,string_415,string_416,string_417,string_418,string_419,string_420,string_421,string_422,string_423,string_424,string_425,string_426,string_427,string_428,string_429,string_430,string_431,string_432,string_433,string_434,string_435,string_436,string_437,string_438,string_439,string_440,string_441,string_442,string_443,string_444,string_445,string_446,string_447,string_448,string_449,string_450,string_451,string_452,string_453,string_454,string_455,string_456,string_457,string_458,string_459,string_460,string_461,string_462,string_463,string_464,string_465,string_466,string_467,string_468,string_469,string_470,string_471,string_472,string_473,string_474,string_475,string_476,string_477,string_478,string_479,string_480,string_481,string_482,string_483,string_484,string_485,string_486,string_487,string_488,string_489,string_490,string_491,string_492,string_493,string_494,string_495,string_496,string_497,string_498,string_499,string_500,string_501,string_502,string_503,string_504,string_505,string_506,string_507,string_508,string_509,string_510,string_511,string_512,string_513,string_514,string_515,string_516,string_517,string_518,string_519,string_520,string_521,string_522,string_523,string_524,string_525,string_526,string_527,string_528,string_529,string_530,string_531,string_532,string_533,string_534,string_535,string_536,string_537,string_538,string_539,string_540,string_541,string_542,string_543,string_544,string_545,string_546,string_547,string_548,string_549,string_550,string_551,string_552,string_553,string_554,string_555,string_556,string_557,string_558,string_559,string_560,string_561,string_562,string_563,string_564,string_565,string_566,string_567,string_568,string_569,string_570,string_571,string_572,string_573,string_574,string_575,string_576,string_577,string_578,string_579,string_580,string_581,string_582,string_583,string_584,string_585,string_586,string_587,string_588,string_589,string_590,string_591,string_592,string_593,string_594,string_595,string_596,string_597,string_598,string_599,string_600,string_601,string_602,string_603,string_604,string_605,string_606,string_607,string_608,string_609,string_610,string_611,string_612,string_613,string_614,string_615,string_616,string_617,string_618,string_619,string_620,string_621,string_622,string_623,string_624,string_625,string_626,string_627,string_628,string_629,string_630,string_631,string_632,string_633,string_634,string_635,string_636,string_637,string_638,string_639,string_640,string_641,string_642,string_643,string_644,string_645,string_646,string_647,string_648,string_649,string_650,string_651,string_652,string_653,string_654,string_655,string_656,string_657,string_658,string_659,string_660,string_661,string_662,string_663,string_664,string_665,string_666,string_667,string_668,string_669,string_670,string_671,string_672,string_673,string_674,string_675,string_676,string_677,string_678,string_679,string_680,string_681,string_682,string_683,string_684,string_685,string_686,string_687,string_688,string_689,string_690,string_691,string_692,string_693,string_694,string_695,string_696,string_697,string_698,string_699,string_700,string_701,string_702,string_703,string_704,string_705,string_706,string_707,string_708,string_709,string_710,string_711,string_712,string_713,string_714,string_715,string_716,string_717,string_718,string_719,string_720,string_721,string_722,string_723,string_724,string_725,string_726,string_727,string_728,string_729,string_730,string_731,string_732,string_733,string_734,string_735,string_736,string_737,string_738,string_739,string_740,string_741,string_742,string_743,string_744,string_745,string_746,string_747,string_748,string_749,string_750,string_751,string_752,string_753,string_754,string_755,string_756,string_757,string_758,string_759,string_760,string_761,string_762,string_763,string_764,string_765,string_766,string_767,string_768,string_769,string_770,string_771,string_772,string_773,string_774,string_775,string_776,string_777,string_778,string_779,string_780,string_781,string_782,string_783,string_784,string_785,string_786,string_787,string_788,string_789,string_790,string_791,string_792,string_793,string_794,string_795,string_796,string_797,string_798,string_799,string_800,string_801,string_802,string_803,string_804,string_805,string_806,string_807,string_808,string_809,string_810,string_811,string_812,string_813,string_814,string_815,string_816,string_817,string_818,string_819,string_820,string_821,string_822,string_823,string_824,string_825,string_826,string_827,string_828,string_829,string_830,string_831,string_832,string_833,string_834,string_835,string_836,string_837,string_838,string_839,string_840,string_841,string_842,string_843,string_844,string_845,string_846,string_847,string_848,string_849,string_850,string_851,string_852,string_853,string_854,string_855,string_856,string_857,string_858,string_859,string_860,string_861,string_862,string_863,string_864,string_865,string_866,string_867,string_868,string_869,string_870,string_871,string_872,string_873,string_874,string_875,string_876,string_877,string_878,string_879,string_880,string_881,string_882,string_883,string_884,string_885,string_886,string_887,string_888,string_889,string_890,string_891,string_892,string_893,string_894,string_895,string_896,string_897,string_898,string_899,string_900,string_901,string_902,string_903,string_904,string_905,string_906,string_907,string_908,string_909,string_910,string_911,string_912,string_913,string_914,string_915,string_916,string_917,string_918,string_919,string_920,string_921,string_922,string_923,string_924,string_925,string_926,string_927,string_928,string_929,string_930,string_931,string_932,string_933,string_934,string_935,string_936,string_937,string_938,string_939,string_940,string_941,string_942,string_943,string_944,string_945,string_946,string_947,string_948,string_949,string_950,string_951,string_952,string_953,string_954,string_955,string_956,string_957,string_958,string_959,string_960,string_961,string_962,string_963,string_964,string_965,string_966,string_967,string_968,string_969,string_970,string_971,string_972,string_973,string_974,string_975,string_976,string_977,string_978,string_979,string_980,string_981,string_982,string_983,string_984,string_985,string_986,string_987,string_988,string_989,string_990,string_991,string_992,string_993,string_994,string_995,string_996,string_997,string_998,string_999,string_1000,string_1001,string_1002,string_1003,string_1004,string_1005,string_1006,string_1007,string_1008,string_1009,string_1010,string_1011,string_1012,string_1013,string_1014,string_1015,string_1016,string_1017,string_1018,string_1019,string_1020,string_1021,string_1022,string_1023,string_1024,string_1025,string_1026,string_1027,string_1028,string_1029,string_1030,string_1031,string_1032,string_1033,string_1034,string_1035,string_1036,string_1037,string_1038,string_1039,string_1040,string_1041,string_1042,string_1043,string_1044,string_1045,string_1046,string_1047,string_1048,string_1049,string_1050,string_1051,string_1052,string_1053,string_1054,string_1055,string_1056,string_1057,string_1058,string_1059,string_1060,string_1061,string_1062,string_1063,string_1064,string_1065,string_1066,string_1067,string_1068,string_1069,string_1070,string_1071,string_1072,string_1073,string_1074,string_1075,string_1076,string_1077,string_1078,string_1079,string_1080,string_1081,string_1082,string_1083,string_1084,string_1085,string_1086,string_1087,string_1088,string_1089,string_1090,string_1091,string_1092,string_1093,string_1094,string_1095,string_1096,string_1097,string_1098,string_1099,string_1100,string_1101,string_1102,string_1103,string_1104,string_1105,string_1106,string_1107,string_1108,string_1109,string_1110,string_1111,string_1112,string_1113,string_1114,string_1115,string_1116,string_1117,string_1118,string_1119,string_1120,string_1121,string_1122,string_1123,string_1124,string_1125,string_1126,string_1127,string_1128,string_1129,string_1130,string_1131,string_1132,string_1133,string_1134,string_1135,string_1136,string_1137,string_1138,string_1139,string_1140,string_1141,string_1142,string_1143,string_1144,string_1145,string_1146,string_1147,string_1148,string_1149,string_1150,string_1151,string_1152,string_1153,string_1154,string_1155,string_1156,string_1157,string_1158,string_1159,string_1160,string_1161,string_1162,string_1163,string_1164,string_1165,string_1166,string_1167,string_1168,string_1169,string_1170,string_1171,string_1172,string_1173,string_1174,string_1175,string_1176,string_1177,string_1178,string_1179,string_1180,string_1181,string_1182,string_1183,string_1184,string_1185,string_1186,string_1187,string_1188,string_1189,string_1190,string_1191,string_1192,string_1193,string_1194,string_1195,string_1196,string_1197,string_1198};

char buffer[100];






//String TRIGRAMS [] = {"SPACE\0","a\0","abdomen\0","able/ability\0","abort-s-ed-ing\0","about\0","above\0","accident-al-s\0","accomplish-ed\0","accomplishing\0","ache\0","acknowledge\0","act-ion-ing-s\0","act-ive-ivity-s\0","add-ed-itional\0","add-ing-s\0","adjacent\0","administration\0","administrative\0","admit\0","advance-d-ing\0","after\0","age\0","agent-s\0","agree\0","air (fld/port)\0","airborne df\0","aircraft\0","airdrop-s\0","airmobile\0","alarm\0","ALE\0","alert-ed-ing\0","alive\0","all\0","alley\0","alt supply pt\0","alternate\0","alt ammo\0","altitude\0","am\0","am in pos (to)\0","amateur\0","ambulance\0","ambush-ed-ing\0","ammunition\0","amplitude modulation\0","amputate\0","an \0","and\0","answer-d-ing-s\0","antenna\0","anti-\0","apply\0","approach-ed-s\0","approach-ing\0","approve-al-d-ing\0","approximate-ly\0","April\0","are/is\0","area-s\0","arm-s-ed\0","army-ies\0","around\0","arrange-d-ing\0","arrange-ment\0","arrive-al-d-ing\0","arrow\0","article\0","as\0","asap\0","ask\0","assault\0","assemble-d-ing\0","assist-ance\0","assist-ed-ing\0","at\0","at (once)\0","atlantic\0","attach-ed-ing\0","attach-ment\0","attack-ed-ing-s\0","August\0","authorization\0","authorize-d-ing\0","automatic\0","automobile\0","aviator/pilot\0","axe\0","axis (of)\0","azimuth (of)\0","b\0","back-ed-ing\0","bad\0","ball\0","band\0","bank\0","barbed wire\0","barometer\0","barrage-s\0","barrier\0","base-d-s-ing\0","battalion-s\0","battery charger\0","bed\0","been\0","beer\0","before\0","begin\0","below\0","belt\0","between\0","beyond\0","bike\0","binoculars\0","biological\0","bit\0","bite\0","bivouac-ed-ing\0","black\0","bleed\0","blister\0","block-ed-ing\0","blow-ing (up)\0","blow-n\0","blue\0","boat-s\0","bomb-d-r-ing-s\0","bone\0","boobytrap\0","book\0","boots\0","border\0","boundary-ies\0","bow\0","box\0","boy\0","break/broken\0","breakfast\0","breast\0","bridge-d-ing-s\0","brother\0","bug(s)\0","building-s\0","bulldozer\0","bunker-s\0","burst-ing-s\0","but\0","by\0","bypass-ed-ing-s\0","c\0","cable-s\0","cache\0","caliber\0","call\0","camera\0","camouflage-d\0","camouflage-ing\0","camp\0","can\0","can\0","canal-s\0","cancel-led-s\0","candle\0","capable-ity\0","capacity-ties\0","capsule\0","capture-d-ing\0","car\0","carry-ied-iers\0","casualty-ies\0","cave\0","CB radio\0","cease-s-d-ing\0","challenge-d-ing\0","chance\0","change\0","change cipher\0","channel\0","charge-d-s\0","check-d-ing-s\0","checkpoint\0","chemical-s\0","child-ren\0","church\0","circle\0","city\0","civilian-s\0","clarification(of)\0","class-ify\0","classification\0","clean-ed-ing\0","clear-ed-ance\0","clearing-s\0","close-d-ing\0","clothe-es-ing\0","coast-s-al\0","coffee\0","collapse\0","collect-ed-ion\0","collect-ing-s\0","column-s\0","combat\0","come-ing\0","comma\0","command-er-ed-ing-s\0","commit-ment\0","commit-ted-ing\0","communicate-d-ions-s\0","company\0","complete-d-ing\0","complete-ion\0","compound\0","compromise-d-ing\0","computer\0","concentrate-d-ing\0","concentrate-s-ion\0","condition-ed-ing\0","conduct-ed-ing\0","confidential\0","connect-ed-ing\0","connect-ion\0","conservation\0","conserve-d\0","consolidate-d\0","consolidate-ing\0","consolidation\0","contact-ed-s\0","contact-ing\0","contaminate-d\0","contaminate-ion-ing\0","continue-ation\0","continue-d-ing\0","control-ed-ing-s\0","conversation\0","convoy-s\0","cook\0","coord-s-d-ing\0","corporation\0","corps\0","correct (me)\0","correct-ed-ing\0","cost\0","could\0","counterattack-ed-s\0","counterattack-ing\0","counterpart\0","cover-ed-ing\0","craft\0","crane\0","critical-ly\0","cross-ed-ing\0","crossroad-s\0","crushed\0","crystal\0","CTCSS\0","culvert\0","cup\0","cut-off\0","CW\0","d\0","damage-d-ing\0","danger\0","dangerous\0","darkness\0","day-s/date-s\0","deadline-d-ing\0","death\0","December\0","deception\0","decontaminate-d-ion\0","decrease-d-ing\0","deer\0","defend-ed-g-s\0","defense-sive\0","degree-s\0","delay-ed-ing-s\0","delete-d-ion\0","deliver-ed-ing\0","demolition\0","demonstrate-d-ing\0","demonstrate-d-s-ion\0","deny-ied-ies\0","depart-ed-ing-ure\0","deploy-ed-ing\0","deploy-ment-s\0","depot\0","deputy-ies\0","designate-d\0","designate-ion\0","desk\0","destination\0","destroy-d-ing-s\0","detach-ed-es\0","detach-ment-s\0","determine\0","diesel\0","dig/dug (in)\0","dinner\0","direct-d-ion-ing\0","direction finding\0","disable-d-ing\0","disapprove-d-al\0","disperse-d-ing-al\0","displace-d-ing\0","displace-ment\0","dispose-d-al\0","disregard-ed-ing\0","distance-s\0","district-s\0","ditch\0","divert-ed-ion\0","divide\0","division-s\0","do\0","dog\0","down-ed\0","downed acft\0","drill drip\0","drive\0","driveway\0","drop-ping-ped\0","drug-s\0","DTMF\0","due\0","dump-ed-ing\0","during\0","e\0","east-ern (of)\0","ed\0","effect-ed-ing\0","effect-ive-s\0","eight\0","electric-al-ity\0","element-s\0","elevate-d-ion\0","eliminate-ed-ing-s\0","elk\0","email\0","embank-ment\0","embrace-d-ing\0","emergency\0","emplace-ment\0","employ-ed-ing\0","en\0","encounter-d-ing\0","encrypt-ed-ion\0","end-ed-ing\0","enemy\0","engine\0","engineer-d-ing-s\0","enlist-ed-ing\0","entrench-ed\0","envelop-ed-ing\0","envelope\0","equip-ing-s\0","er\0","error\0","es\0","escape-d-ing\0","estab-ed-contact at\0","establish-ing\0","estimat-ion\0","estimate-d-ing\0","et\0","eta your loc\0","etd\0","evac-d-ing-ion\0","evasion\0","execute-d-ing\0","execute-ion-s\0","exercise\0","exhaust-ed-ing\0","expect-ation-s\0","expect-ed-ing\0","expedite-d-ing\0","explode-d-s\0","exploit-ed-ing\0","explosive-s\0","expose-d-ing\0","extend-d-g-ive\0","extend-extent\0","extend-sion\0","extra\0","extract-s-ed-ing\0","f\0","facility\0","fade-ed-ing\0","fail-ed-ing\0","fallout\0","family\0","far\0","fatal\0","father\0","favor-able-ing\0","favor-s-ed\0","February\0","feet/foot\0","FeldHell\0","FEMA\0","field-s\0","fight-er-ing\0","final\0","fire-d-ing-s\0","fish\0","five\0","flame-d-ing-s\0","flank-ed-ing-s\0","flare-d-s\0","fled\0","flesh\0","flexible-ity\0","flight\0","foe\0","fog\0","fold-ing\0","follow-ed-ing\0","food\0","for\0","force-s-d-ing\0","ford-able\0","forearm\0","forest-s\0","fortify-ication\0","fortify-ied\0","forward-ed-ing\0","found\0","four\0","fr\0","fracture\0","frag\0","freedom\0","freeze-ing\0","frequency modulation\0","frequency-ies\0","Friday\0","friend-ly\0","from\0","front-age-ally\0","FRS\0","fruit\0","fuel\0","fuse-d\0","future\0","g\0","gallon-s\0","gas-ing-ed\0","gasoline\0","gate\0","general-ize\0","generator(set)\0","get-ting\0","girl\0","give-n-ing\0","glass\0","GMRS\0","go-ing(to)\0","good\0","government\0","GPS\0","grade-d-ing\0","great\0","green\0","grid(coord)\0","ground-s-ed\0","group\0","guard-ed-ing-s\0","guide-ance\0","guide-d-s-ing\0","gunpowder\0","guns-s\0","h\0","had\0","halt-ed\0","Ham/ham\0","hammer\0","hand\0","handbook\0","handie-talkie\0","harass-ed-ing\0","harass-ment\0","hate\0","have/has\0","he\0","head-ed-ing\0","headphones\0","hear-d\0","heavy\0","held\0","helicopter-s\0","her\0","here\0","hidden\0","hide\0","high speed burst\0","high-er-est\0","highway-s\0","hill/mt/rise-s\0","him\0","his\0","hit-tin\0","hold-er-ing\0","hole\0","home\0","hospital-s\0","hostile\0","hour-s-ly\0","how\0","HQ\0","hundred\0","i\0","ice\0","identification\0","identify-ed\0","IDY\0","ied\0","ies\0","if\0","ill-ness\0","immediately\0","imminent\0","immobile-ize-d-ing\0","impact\0","impassible\0","impossible\0","improve-d-ing\0","improve-ment\0","improvised\0","in\0","in-accordance-with\0","inadequate\0","inch-es\0","incident-al-s\0","increase-d-ing-s\0","indigenous\0","indirect\0","individual\0","infantry\0","infiltrate-d-r-s\0","infiltrate-g-ion\0","inflict\0","inform-d-ation\0","infrared\0","ing\0","initial-ed-ly\0","insect\0","insert-s-ed-ing\0","install-d-ation\0","instrumental\0","intact\0","intend-ed-tion\0","intercept-d-or\0","intercept-ion-s\0","interfere-d-ing\0","interfere-nce\0","internal\0","interrogate-d\0","interrogate-ion\0","intersection\0","interval\0","is\0","isolate-d-ing\0","issue-d-ing-s\0","it\0","item-s\0","j\0","jacket\0","jam-med-ing\0","January\0","jeep\0","job\0","join-ed-ing\0","joint\0","July\0","jump-ed-ing (off)\0","junction-s(road)\0","June\0","jury\0","just\0","k\0","keep-s-ing\0","kerosene\0","key\0","kidney\0","kidney\0","kill\0","kill\0","killed in act\0","kilometer-s\0","kit\0","knife\0","knot\0","know-n-ing\0","knowledge\0","L\0","labor-ed-ing\0","lacerate\0","lamp\0","land-ed-ing\0","large\0","last\0","lateral\0","launch-d-r-ing\0","law\0","lay/laid\0","lead-er-ing\0","leaflet-s\0","least\0","leave/left\0","left (of)\0","leg\0","letter\0","level\0","liaison\0","library\0","life\0","ligh-er-ing-d-s\0","like-s\0","limit-ed-ing-s\0","line-d-s (of)\0","list\0","listen-ed-ing\0","litter-s\0","load-s-ed\0","local-ize-d\0","locate-d-ing-ions\0","location (of)\0","lock\0","log\0","logistic-al-s\0","look (for)\0","loss-es-t\0","loudspeaker\0","love\0","lowe-er-est\0","lower side band\0","lunch\0","ly\0","m\0","machinegun-s\0","made\0","magnetic\0","magnify-ing\0","main\0","main body\0","main supply rt\0","maintain-ed\0","maintain-ing-s\0","maintenance\0","make-ing/made\0","male\0","man-ned-ning\0","maneuver-ing-s\0","manual\0","many\0","map-ped-ping-s\0","March/march\0","market\0","MARS\0","match-ed-s-ing\0","max (range)\0","May\0","me\0","meal\0","means\0","measure-d\0","measurement\0","meat\0","mechanic-al\0","mechanize-d\0","medical\0","medium\0","medivac needed\0","meet (me at)\0","meet-ing\0","message-s\0","messenger\0","meter-s\0","MFSK\0","microphone\0","might\0","mile-s\0","milk\0","mine-d(field)\0","minimize-d\0","minimum\0","minor\0","minute(s)\0","miss-ed-ing\0","missile-s\0","missing in act\0","mission-s\0","mobile-ity\0","modem\0","modulation\0","Monday\0","money\0","moon\0","morale\0","more\0","morning\0","morse\0","most\0","mother\0","motor-ized\0","mount-ed-ing\0","mountain-ous\0","move-d-ing\0","move-ment\0","MRE\0","multiple\0","music\0","my\0","my location is\0","n\0","nail\0","narrow\0","near\0","need-ed-ing\0","net-ted-ing\0","network\0","neutral\0","neutralize-d-ing\0","new\0","news\0","newspaper\0","night vision\0","night-s\0","nine\0","no fire line\0","no/non/neg\0","none\0","north-ern(of)\0","not\0","not later than\0","note\0","notebook\0","nothing\0","notify-ed-s\0","November\0","now\0","nuclear\0","number-s\0","o\0","objective-s\0","observation post\0","observation-s\0","observe-d-r\0","observe-s-ing\0","obstacle-s\0","occupy-ed-ing\0","October\0","odor\0","of\0","offense-ive\0","officer-s\0","oil\0","on\0","one\0","only\0","open-ed-ing\0","operate-s-d-ing\0","operation-al\0","opportunity-s\0","or\0","orange\0","order-ed\0","ordnance\0","organize-ation\0","organize-d\0","orient-ing-ation\0","origin-al-ate\0","other\0","our\0","out (of)\0","outpost\0","over-age\0","over-run\0","overlay\0","own\0","p\0","pacific\0","packet\0","PACTOR\0","panel-s\0","pants\0","paratroop-s\0","part-s\0","party-s\0","pass-able\0","pass-age-ing\0","password\0","past\0","patrol-ed-ing-s\0","PBBS\0","pen\0","pencil\0","penetrate-d-ing\0","penetration\0","people\0","pepper\0","per\0","percent-age\0","perimeter\0","period\0","permission\0","permit-ed-ing\0","PGP\0","phase\0","photo-er-ed-ing\0","pick\0","pick (up)\0","piece-d-ing-s\0","pipeline\0","pistol\0","place-d-ing\0","plan-s-ed-ing\0","platoons\0","point-s-ed-ing\0","police\0","port(harbor)\0","position-s-ed\0","possible\0","post office\0","post-s\0","postpone-s-ed-ing\0","pound-s\0","powder\0","preparation\0","prepare-d-ing-s\0","prevent\0","priest\0","primary\0","print\0","printer\0","priority\0","privacy\0","private\0","prize-s of war\0","probable\0","process-ed-ing\0","professional\0","progress-ed-ing\0","propane\0","protect-ed-s-ing\0","protect-ive\0","protection\0","provide-d-ing\0","province\0","provision\0","PSK\0","psych\0","pure\0","purification\0","purple\0","pursue-d-ing-t\0","put\0","q\0","quell\0","quest\0","question-ed\0","quiet\0","quit\0","quiz\0","r\0","rad(rad/hr)\0","radar\0","radiation\0","radiator\0","radio-s\0","radiological\0","raid-er-ing-s\0","railhead\0","railroad-s\0","rain\0","range\0","rate\0","ration-s-ed\0","reach-ed-s-ing\0","read\0","ready\0","rear\0","receive-d-er-ing\0","recognize-d-ing\0","recon\0","record\0","recorder\0","recover-ed-y\0","red\0","reduce-ing-tion\0","reference-d-s\0","reference(to)\0","refuge\0","refugee(s)\0","regiment-ed-s\0","registration\0","regroup-ed-ing\0","reinf-ed-s-ing\0","reinforcement(s)\0","relay-ed-ing\0","release-d-ing-s\0","relief/relive\0","remain-ing\0","rendezvous\0","reorganize-d-ation-s\0","repair-ed-ing\0","repeat-ed-ing\0","repeater (radio)\0","repel-ed-ing-s\0","replace-d-ing-s\0","replacement\0","report-ed-ing\0","report-s(to)\0","repulse-d-ing\0","request-d-ing-s\0","require-d-ing\0","requirement\0","rescue\0","reserve-d-ing-s\0","resist-ing-ed\0","resistance\0","rest\0","restore-d-s\0","restrict-ion\0","restrictive\0","result-s-ed-ing\0","resupply-d-s-ing\0","return-ed-ing\0","ridge-d-s\0","rifle-s\0","right(of)\0","riot-s-ed\0","river-stream-s\0","road-s\0","roadblock\0","round-s\0","route-s-d-ing\0","RTTY\0","rucksack\0","rug\0","ruin-s-ed\0","s\0","sad\0","safe-r-ty\0","said\0","salt\0","Saturday\0","saw\0","schedule-d-ing-s\0","school\0","scope\0","scout-ed-ing-s\0","screen-d-ing-s\0","search-d-ing-s\0","second-s-ary\0","secret\0","section-s\0","sector-s\0","secure-d-ing\0","security\0","send/sent-ing\0","separate-d-ion\0","September\0","sequence\0","service-d-able\0","seven\0","shall\0","shell-s-ing-ed\0","shell-s-ing-ed\0","shelter\0","shelter\0","shirt\0","shirt\0","shoot-ing/shot\0","short-ed\0","shortwave\0","shoulder\0","sick\0","sieze-d-ing\0","siezure-s\0","sight-ed-ing\0","sign-ed-ing\0","signal-ed-ing\0","silent-ly-ce\0","simplex\0","simulate-d-ing\0","sister\0","sit/sitrep\0","site-s\0","six\0","sleep-ing\0","slope-s-ing-d\0","slow-ed-ing\0","small-er-est\0","smoke-d-ing-s\0","sniper\0","snow\0","so\0","socks\0","solar\0","solder\0","soldier\0","some\0","soon-er-est\0","sorry\0","sortie-s\0","south-ern(of)\0","speak\0","spearhead\0","spice\0","spine\0","sporadic\0","spot-ted\0","squad-s\0","stand-ing(by)\0","start-ed-ing\0","station-ed-s\0","status(report)\0","stay-ed-ing\0","stike/struck\0","stole-n\0","stop-ped-ing\0","storm\0","storm-ing-s\0","street\0","strength-en\0","strong-er-est\0","submit-ed-ing\0","success-ful-ly\0","such\0","Sunday\0","sunrise\0","sunset\0","superior-ity\0","supplement-ed-ary\0","supply-d-s-ing\0","surface-d-ing\0","surgey\0","surround-ed-ing\0","surveillance\0","survey-ed-s\0","survival\0","suspect-ed-ing\0","swallow-ed(s)\0","switch-ed-ing\0","swollen\0","symmetric\0","t\0","tablet\0","tactic-s-al\0","take-ing/took\0","talk\0","tank destroyer-s\0","tank-er-s\0","tape\0","target-s\0","task(force)\0","taxi\0","team-s-ed\0","tear gas\0","ted\0","teen\0","teeth\0","telephone-s\0","television\0","temple\0","tentative\0","terminate-d-ing\0","terrain\0","territory\0","terrorism\0","terrorists\0","that\0","the\0","their\0","them\0","then\0","there\0","these\0","they\0","this\0","those\0","thousand\0","three\0","THROB\0","through\0","thunder\0","Thursday\0","tide\0","time\0","time-d-ing\0","tion\0","tire\0","to(be)\0","today\0","tomorrow\0","ton-s-age\0","tone\0","tonight\0","tooth\0","top secret\0","total\0","tow-ed-ing\0","toward\0","town/village-s\0","trace-r\0","track-ed-ing\0","traffic\0","trail-er-d-ing-s\0","train-ed-ing-s\0","transmission\0","transmit-ed\0","transport-ed\0","transport-ing-s\0","transportation\0","trapped\0","trouble\0","truck-ed-s-ing\0","Tuesday\0","turn-ed-ing\0","two\0","u\0","unable\0","unarmed\0","unauthorized\0","under\0","undercover\0","understand\0","understood\0","unharmed\0","unidentified\0","unite-d-s-ing\0","until(further notice)\0","unusual\0","up\0","upper side band\0","us\0","use-d-g\0","UTC\0","v\0","vaccine\0","valley\0","vegetable\0","vehicle\0","verification\0","verify-ied\0","very\0","video\0","violate-s-d\0","violet\0","virus\0","visible-ity\0","volt-s\0","voltage\0","vulnerable\0","w\0","wagon\0","wait-ed-ing\0","war\0","warehouse\0","was/were\0","water\0","watts\0","wax\0","waypoint\0","we/us\0","weak-en-ness\0","weapon-s\0","weather\0","Wednesday\0","week-s\0","weekend\0","well\0","west-ern(of)\0","what\0","wheel-ed\0","when\0","where\0","which\0","white\0","who\0","wife\0","wild\0","wilderness\0","will\0","wind\0","WinLink\0","wire-s-d-ing\0","with\0","withdraw-ing-s\0","wood-s-ed\0","work-s-ed-ing\0","Y\0","yellow\0","yet\0","your-r\0","z\0","zero\0","zone-s-ing\0"};
